mgkomitsky/Micromouse/Micromouse/CAD/Fan.SLDPRT

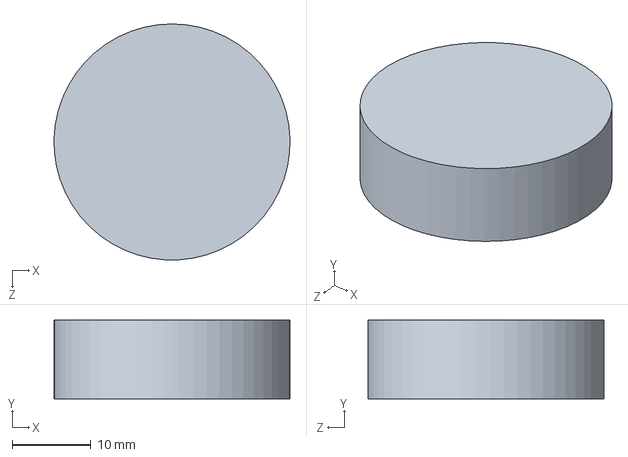
[picture p14: CAD file, 2024-11-20]
Micromouse/CAD/Fan.SLDPRT
30.0 x 10.0 x 30.0 mm
