mgkomitsky/Micromouse/Micromouse/CAD/Wheel.SLDPRT

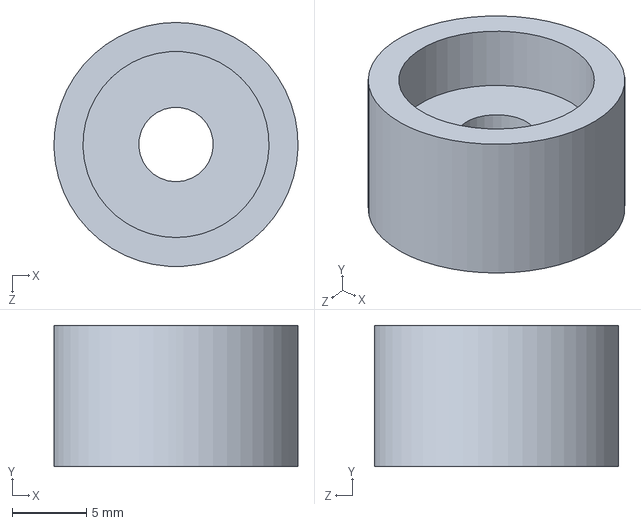
[picture p15: CAD file, 2024-11-20]
Micromouse/CAD/Wheel.SLDPRT
16.4 x 9.50 x 16.4 mm
