mgkomitsky/Micromouse/Micromouse/CAD/Micromouse.SLDASM

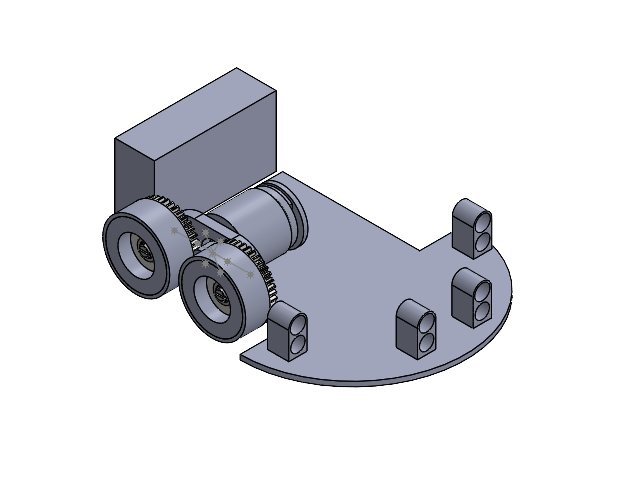
[picture p17: CAD file, 2025-01-04]
Micromouse/CAD/Micromouse.SLDASM
1717T_SR
KHK-US_DS0_5-40 x 2
57155K528_Stainless Steel Ball Bearing x 4
90270A221_Slotted 18-8 Stainless Steel Precision Shoulder Screw x 2
Tire x 2
Wheel_2 x 2
pinion
encoder
motorMount2
Sensor Mounts x 4
Battery
Chassis
